CurtRod/SimpleEVSE-WiFi/include/oled_templates.h

static const unsigned char xbm_locked[] PROGMEM = { /*
 0x00,0x00,0x80,0x03,0x40,0x04,0x20,0x08,0x20,0x08,0x20,0x08,
 0x00,0x00,0xf0,0x1f,0xf0,0x1f,0xf0,0x1f,0xf0,0x1f,0xf0,0x1f,
 0xf0,0x1f,0xf0,0x1f,0xf0,0x1f,0xe0,0x0f}; */
  0xe0,0xf0,0x10,0xf1,0x08,0xf2,0x08,0xf2,0x00,0xf0,0xfc,0xf7,
 0xfc,0xf7,0xfc,0xf7,0xfc,0xf7,0xfc,0xf7,0xfc,0xf7,0xf8,0xf3};

static const unsigned char xbm_unlocked[] PROGMEM = { /*
 0x00,0x00,0x00,0x1c,0x00,0x22,0x00,0x41,0x00,0x41,0x00,0x41,
 0x00,0x00,0xfe,0x03,0xfe,0x03,0xfe,0x03,0xfe,0x03,0xfe,0x03,
 0xfe,0x03,0xfe,0x03,0xfe,0x03,0xfc,0x01}; */
 0x80,0xf3,0x40,0xf4,0x20,0xf8,0x20,0xf8,0x00,0xf8,0xff,0xf0,
 0xff,0xf0,0xff,0xf0,0xff,0xf0,0xff,0xf0,0xff,0xf0,0x7e,0xf0};

static const uint8_t xbm_checked_width = 73;
static const uint8_t xbm_checked_height = 60;
static const unsigned char xbm_checked[] PROGMEM = {
 0x00,0x00,0x00,0x00,0x00,0x00,0x00,0x30,0x00,0xfe,0x00,0x00,
 0x00,0x00,0x00,0x00,0x00,0x78,0x00,0xfe,0x00,0x00,0x00,0x00,
 0x00,0x00,0x00,0xfc,0x00,0xfe,0x00,0x00,0x00,0x00,0x00,0x00,
 0x00,0xfe,0x01,0xfe,0x00,0x00,0x00,0x00,0x00,0x00,0x00,0xff,
 0x03,0xfe,0x00,0x00,0x00,0x00,0x00,0x00,0x80,0xff,0x07,0xfe,
 0x00,0x00,0x00,0x00,0x00,0x00,0xc0,0xff,0x0f,0xfe,0x00,0x00,
 0x00,0x00,0x00,0x00,0xe0,0xff,0x1f,0xfe,0x00,0x00,0x00,0x00,
 0x00,0x00,0xf0,0xff,0x3f,0xfe,0x00,0x00,0x00,0x00,0x00,0x00,
 0xf8,0xff,0x7f,0xfe,0x00,0x00,0x00,0x00,0x00,0x00,0xfc,0xff,
 0xff,0xfe,0x00,0x00,0x00,0x00,0x00,0x00,0xfe,0xff,0xff,0xff,
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
 0xe0,0x03,0xf0,0x0f,0xe0,0x0f,0x80,0x04,0xc0,0x03,0xe0,0x07,
 0xc0,0x07,0xc0,0x02,0x80,0x07,0x00,0x00,0x00,0x00,0x60,0x03,
 0x80,0x0f,0x00,0x00,0x00,0x00,0x30,0x01,0x00,0x1f,0x00,0x00,
 0x00,0x00,0x98,0x00,0x00,0x3e,0x00,0x00,0x00,0x00,0x48,0x00,
 0x00,0x3c,0x00,0x00,0x00,0x00,0x28,0x00,0x00,0x18,0x00,0x00,
 0x00,0x00,0x18,0x00,0x00,0x80,0x07,0x00,0x00,0xc0,0x01,0x00,
 0x00,0x80,0x0f,0x00,0x00,0xf0,0x01,0x00,0x00,0x80,0x7f,0x00,
 0x00,0xfc,0x01,0x00,0x00,0x00,0xfe,0x07,0xc0,0xff,0x00,0x00,
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
